dish-glitch/Microgrid-Home-Energy-Monitor/docs/photos/image-1781241379972.png

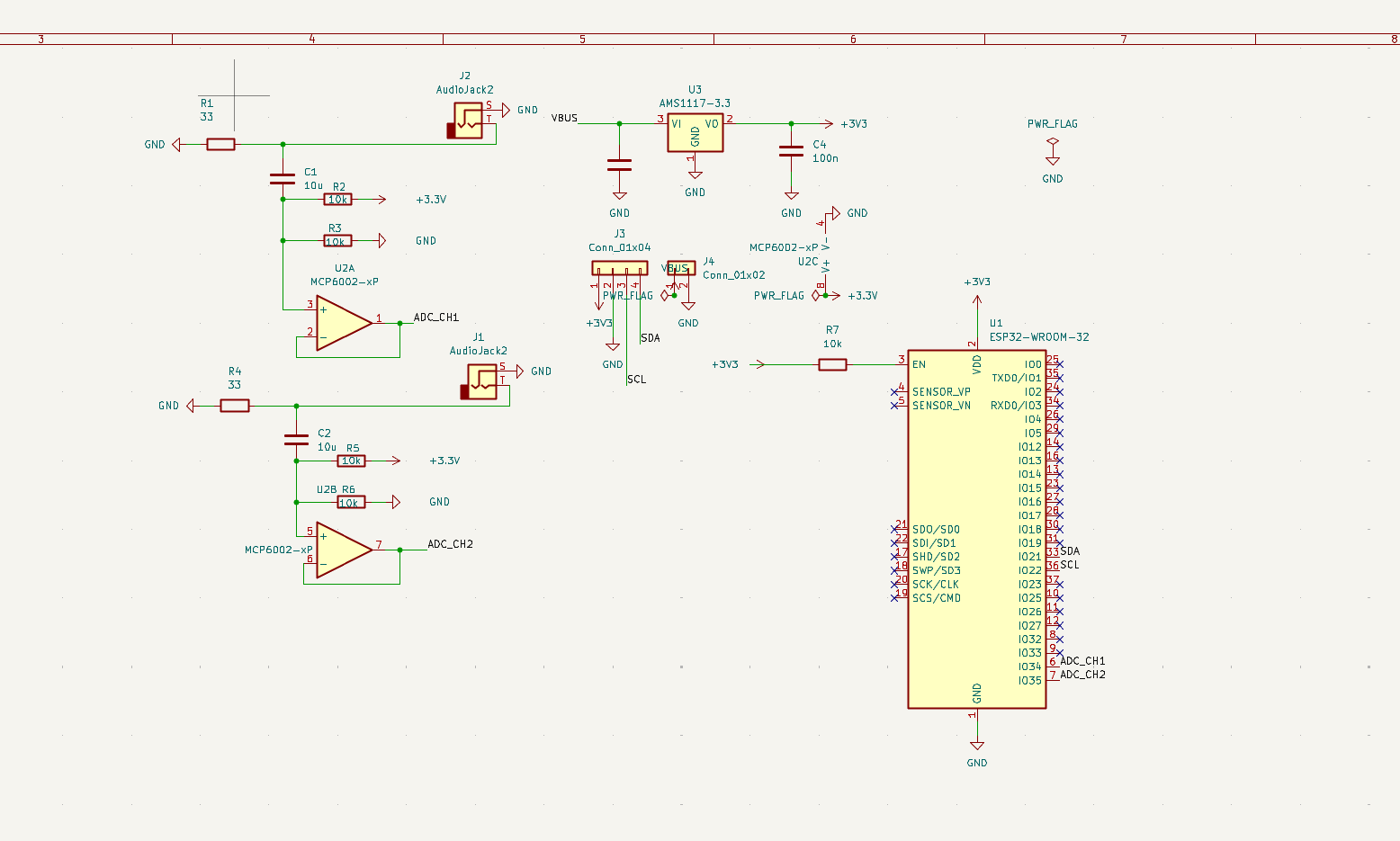
docs/photos/image-1781241379972.png
