dish-glitch/Microgrid-Home-Energy-Monitor/docs/photos/image-1781640762124.webp

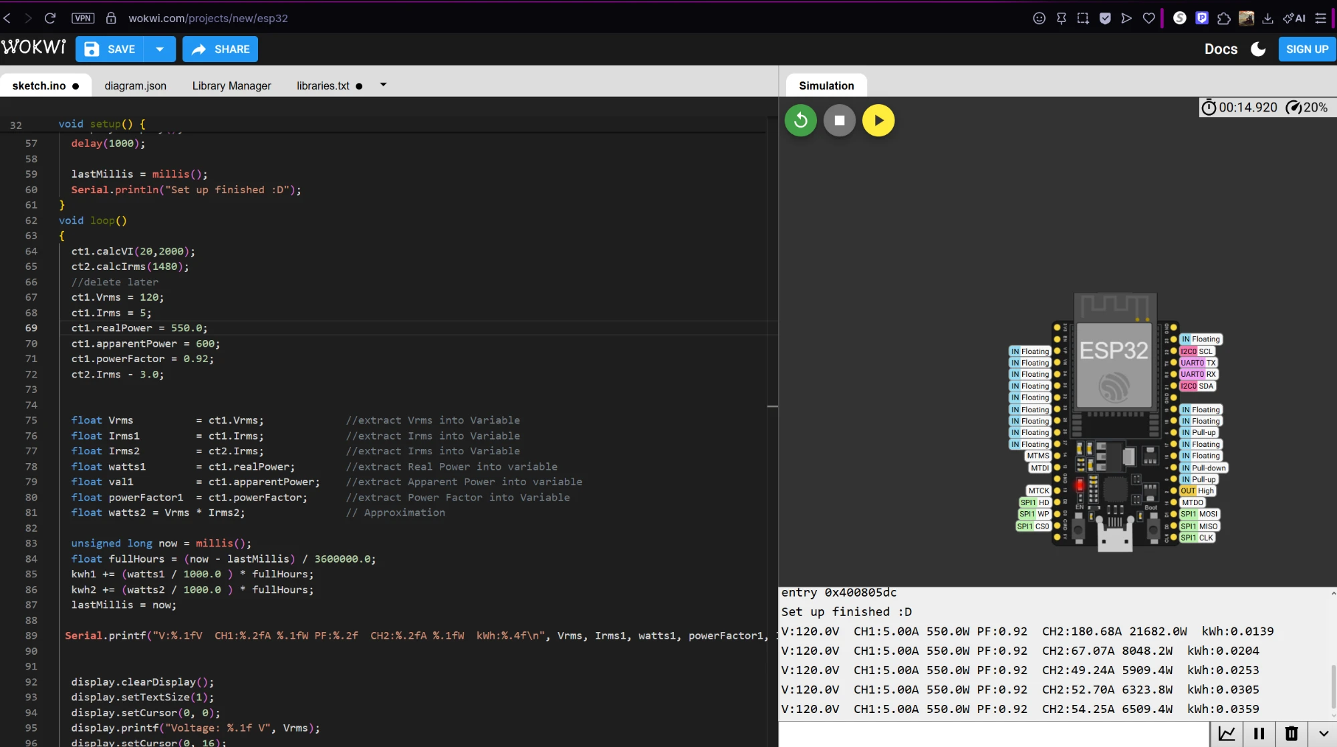
docs/photos/image-1781640762124.webp
