dish-glitch/Microgrid-Home-Energy-Monitor/docs/photos/image-1781640787115.png

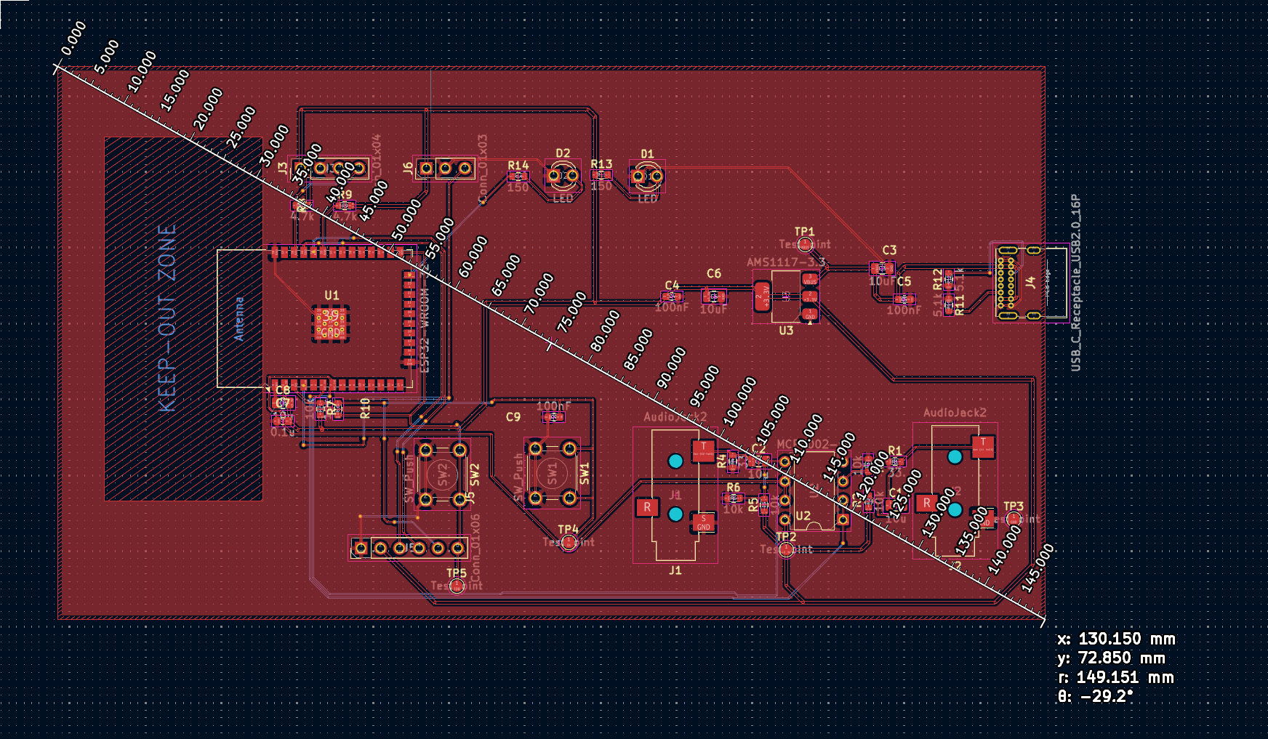
docs/photos/image-1781640787115.png
