dish-glitch/Microgrid-Home-Energy-Monitor/docs/photos/image-1781640804988.png

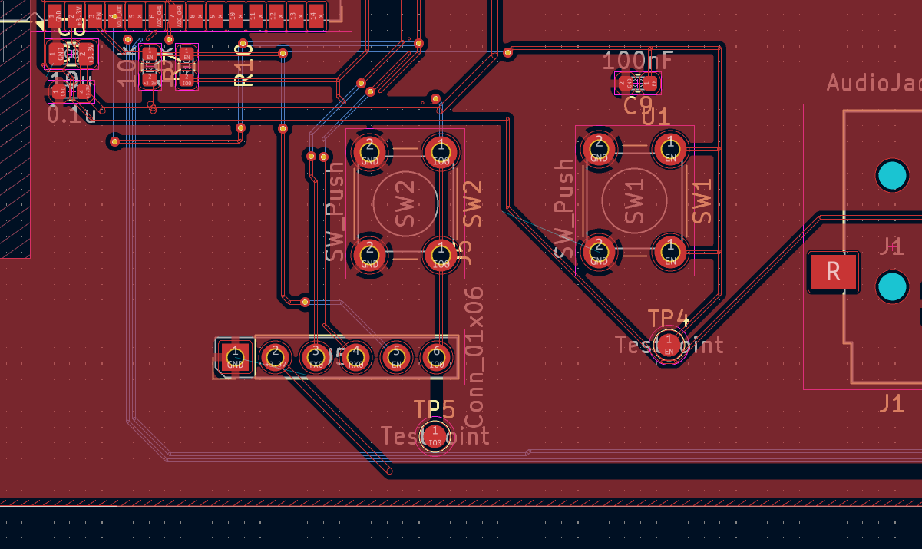
docs/photos/image-1781640804988.png
