dish-glitch/Microgrid-Home-Energy-Monitor/docs/photos/image-1781640816486.png

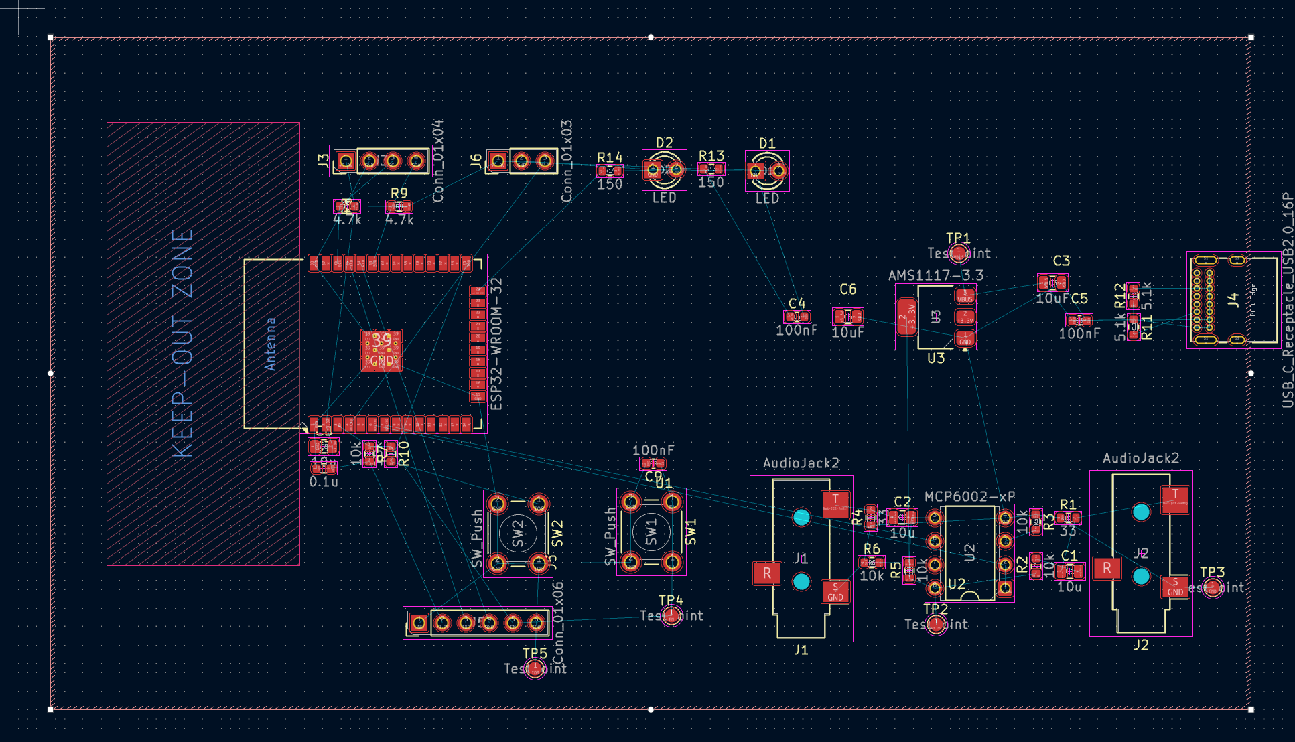
docs/photos/image-1781640816486.png
