dish-glitch/Microgrid-Home-Energy-Monitor/docs/photos/image-1781640849859.png

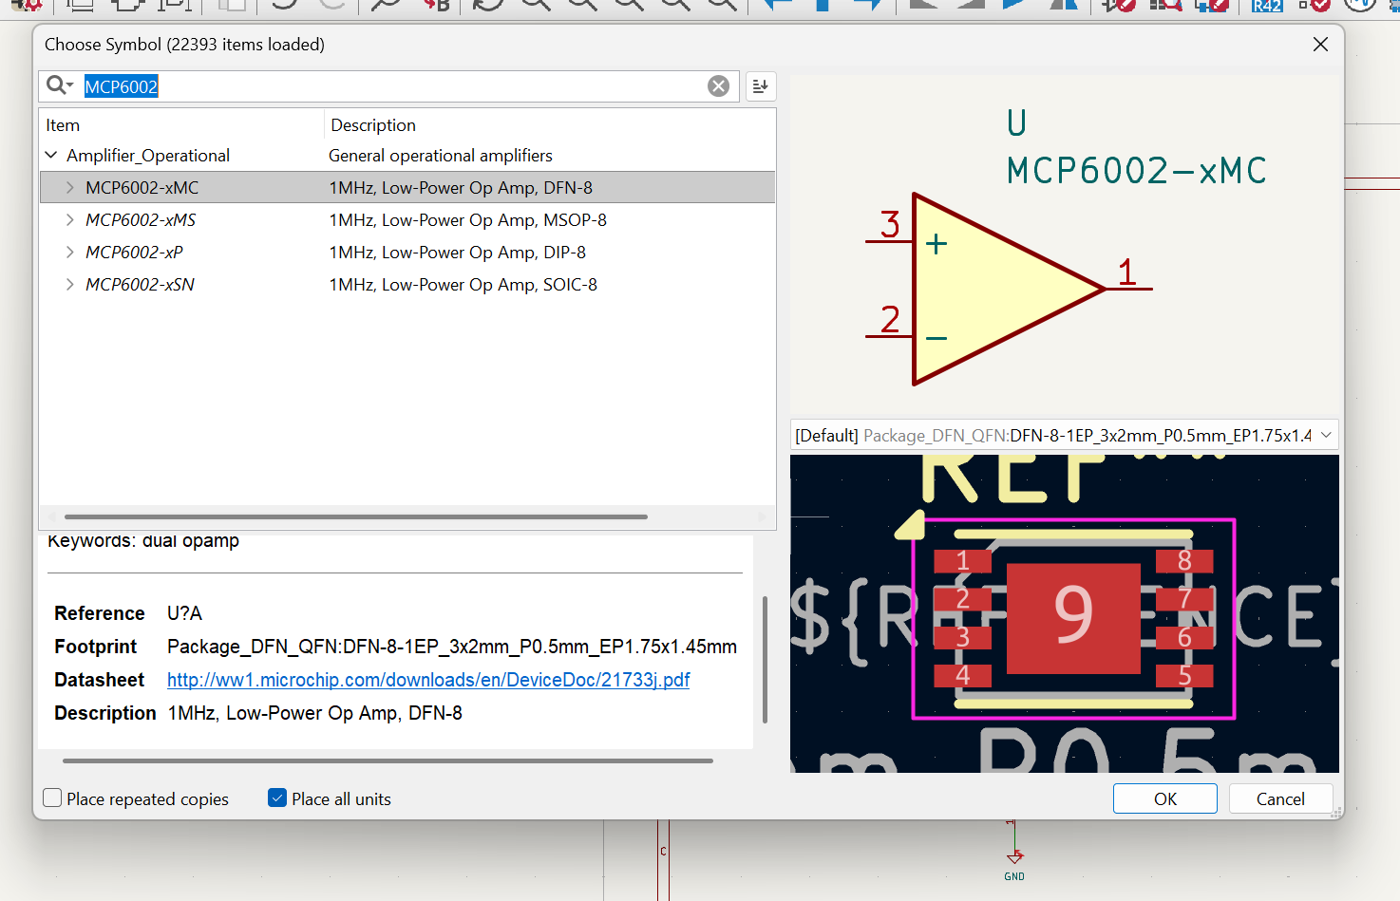
docs/photos/image-1781640849859.png
